heligone/spinorialBall/STL/Soccer_ball_Truncated_icosahedron_assembly/images/83c5e83ae44e08008ed81e9d2f102d47_preview_featured.jpg

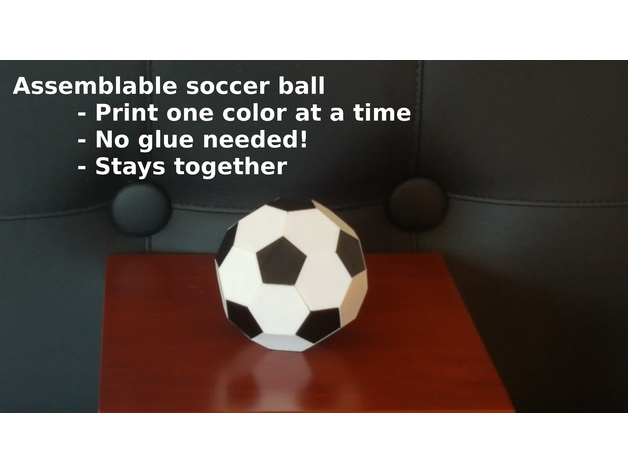
STL/Soccer_ball_Truncated_icosahedron_assembly/images/83c5e83ae44e08008ed81e9d2f102d47_preview_featured.jpg
