heligone/spinorialBall/STL/Soccer_ball_Truncated_icosahedron_assembly/images/a78be3f28a5d14c5ceab12fbc726420b_preview_featured.jpg

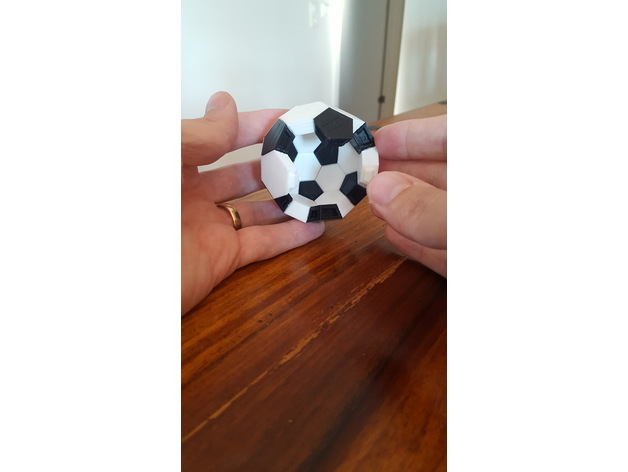
STL/Soccer_ball_Truncated_icosahedron_assembly/images/a78be3f28a5d14c5ceab12fbc726420b_preview_featured.jpg
