heligone/spinorialBall/STL/Soccer_ball_Truncated_icosahedron_assembly/images/b8bacaaa4351ee0689ca10c400ba891b_preview_featured.jpg

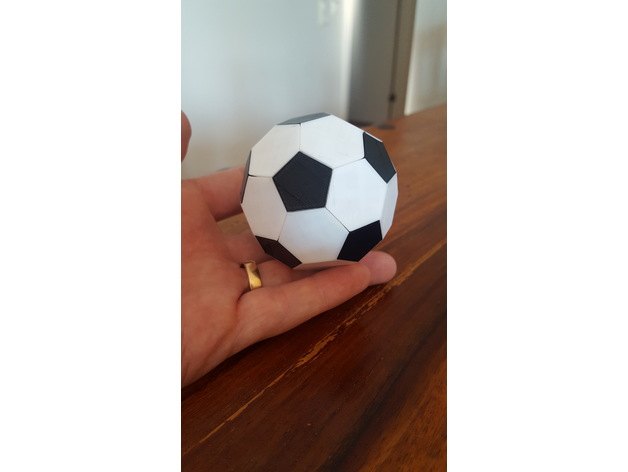
STL/Soccer_ball_Truncated_icosahedron_assembly/images/b8bacaaa4351ee0689ca10c400ba891b_preview_featured.jpg
